QuinnLoewen/Teensy-Synth-Project/Documentation/a-minor-arpeggio.jpg

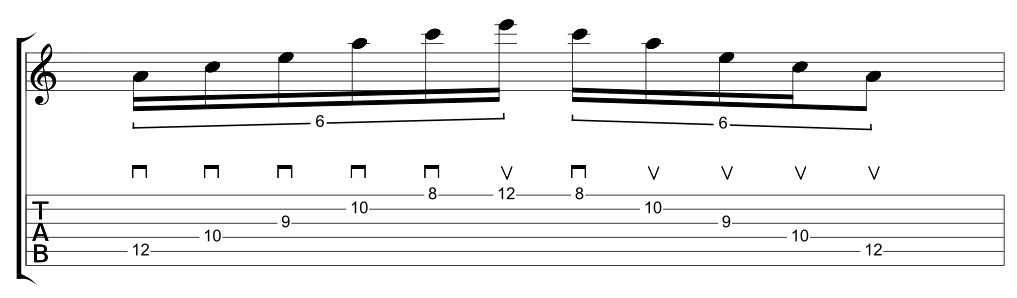
Documentation/a-minor-arpeggio.jpg
