QuinnLoewen/Teensy-Synth-Project/Documentation/Signal Mixing.png

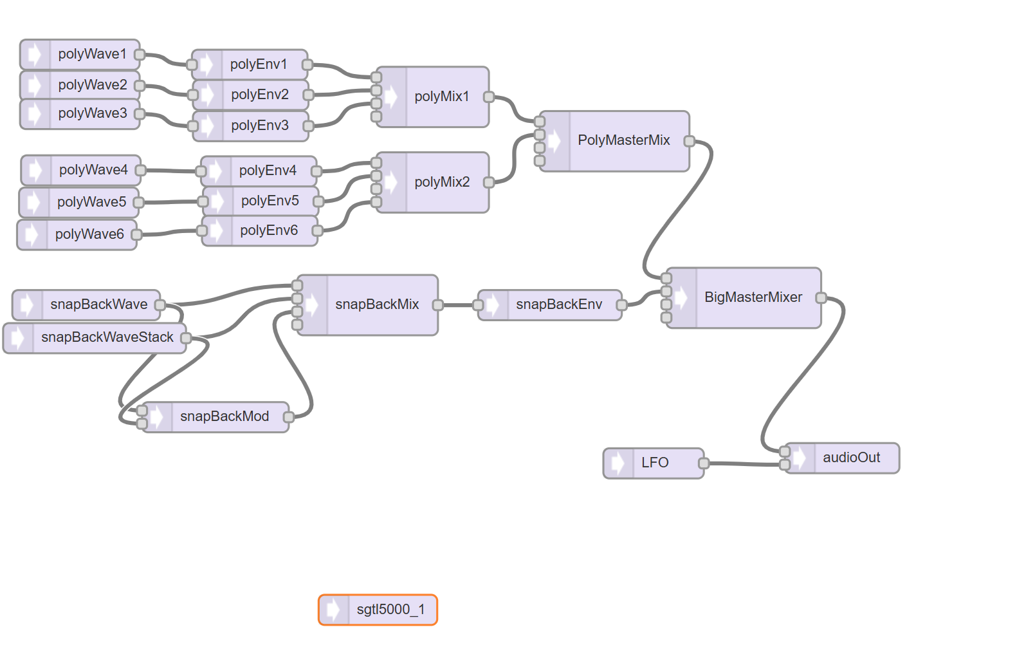
Documentation/Signal Mixing.png
