QuinnLoewen/Teensy-Synth-Project/Documentation/Software_Flowchart.png

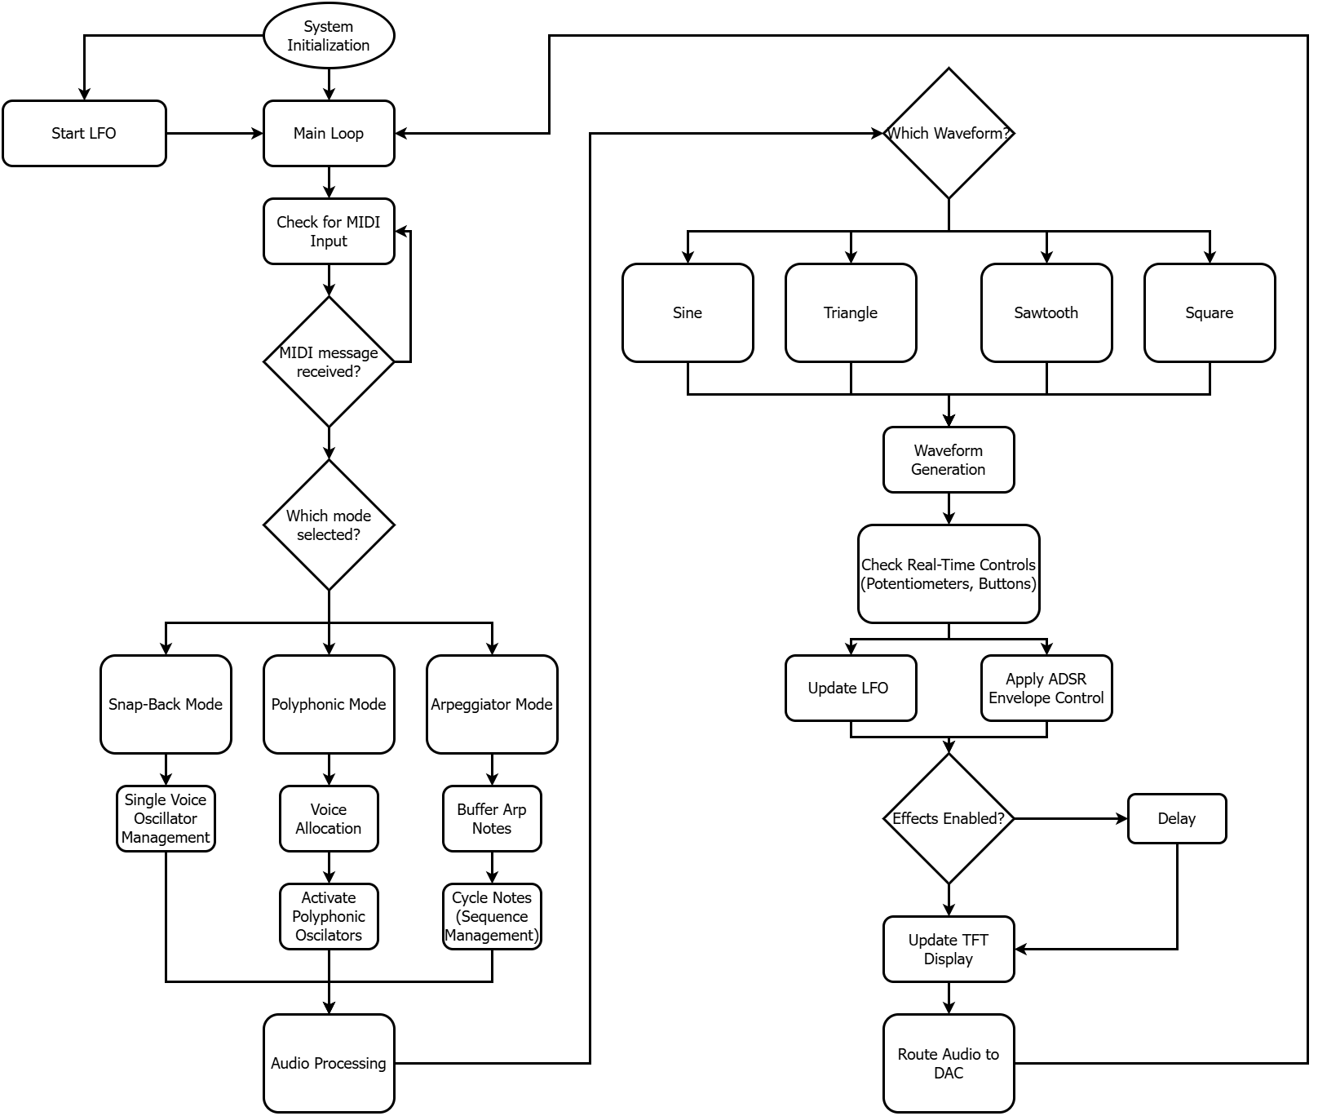
Documentation/Software_Flowchart.png
