QuinnLoewen/Teensy-Synth-Project/Documentation/stackedsine.png

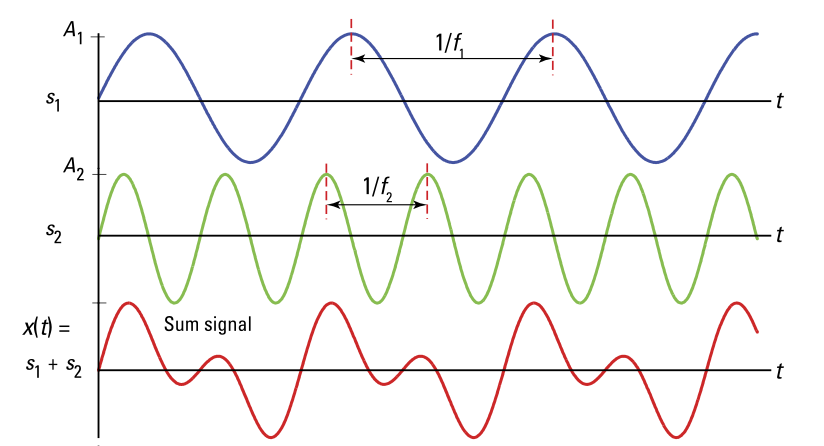
Documentation/stackedsine.png
