QuinnLoewen/Teensy-Synth-Project/Documentation/System_Architecture.png

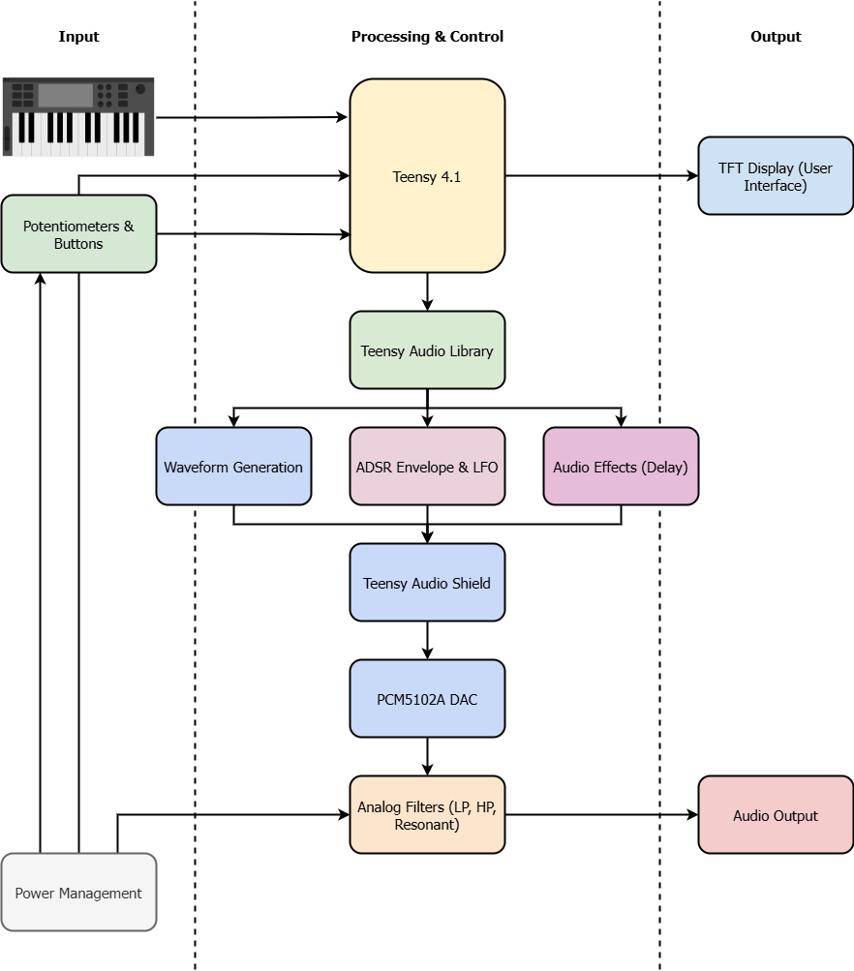
Documentation/System_Architecture.png
