QuinnLoewen/Teensy-Synth-Project/Documentation/waveform_types.png

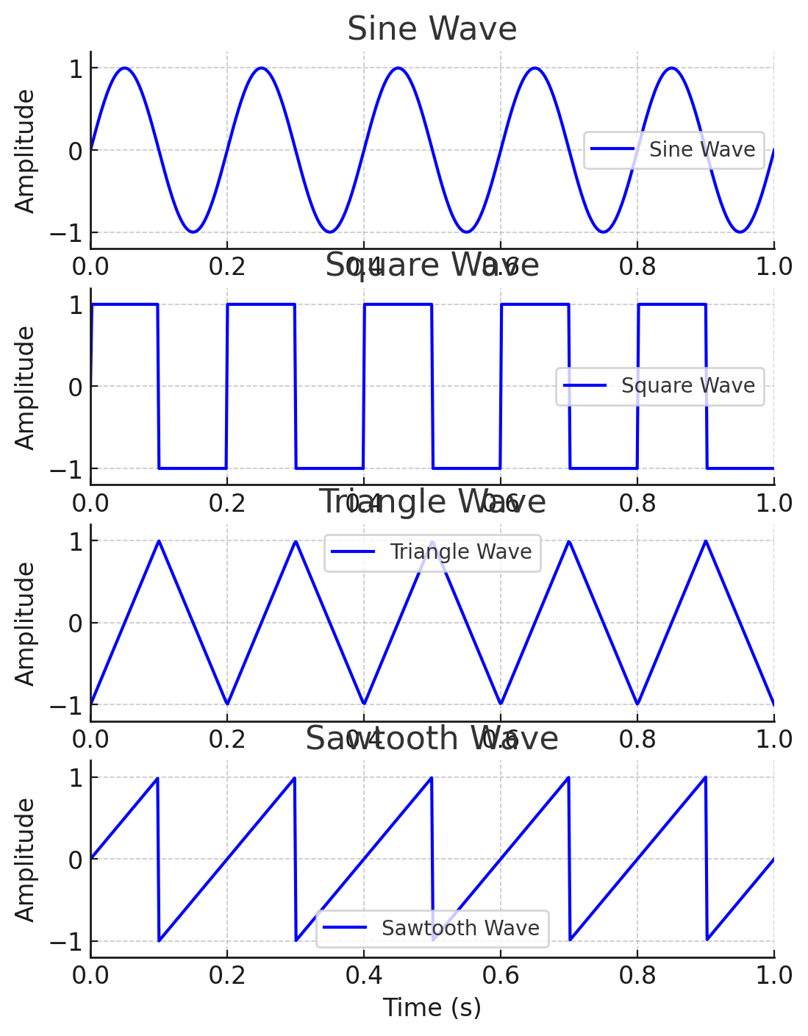
Documentation/waveform_types.png
