QuinnLoewen/Teensy-Synth-Project/Documentation/Waveforms.png

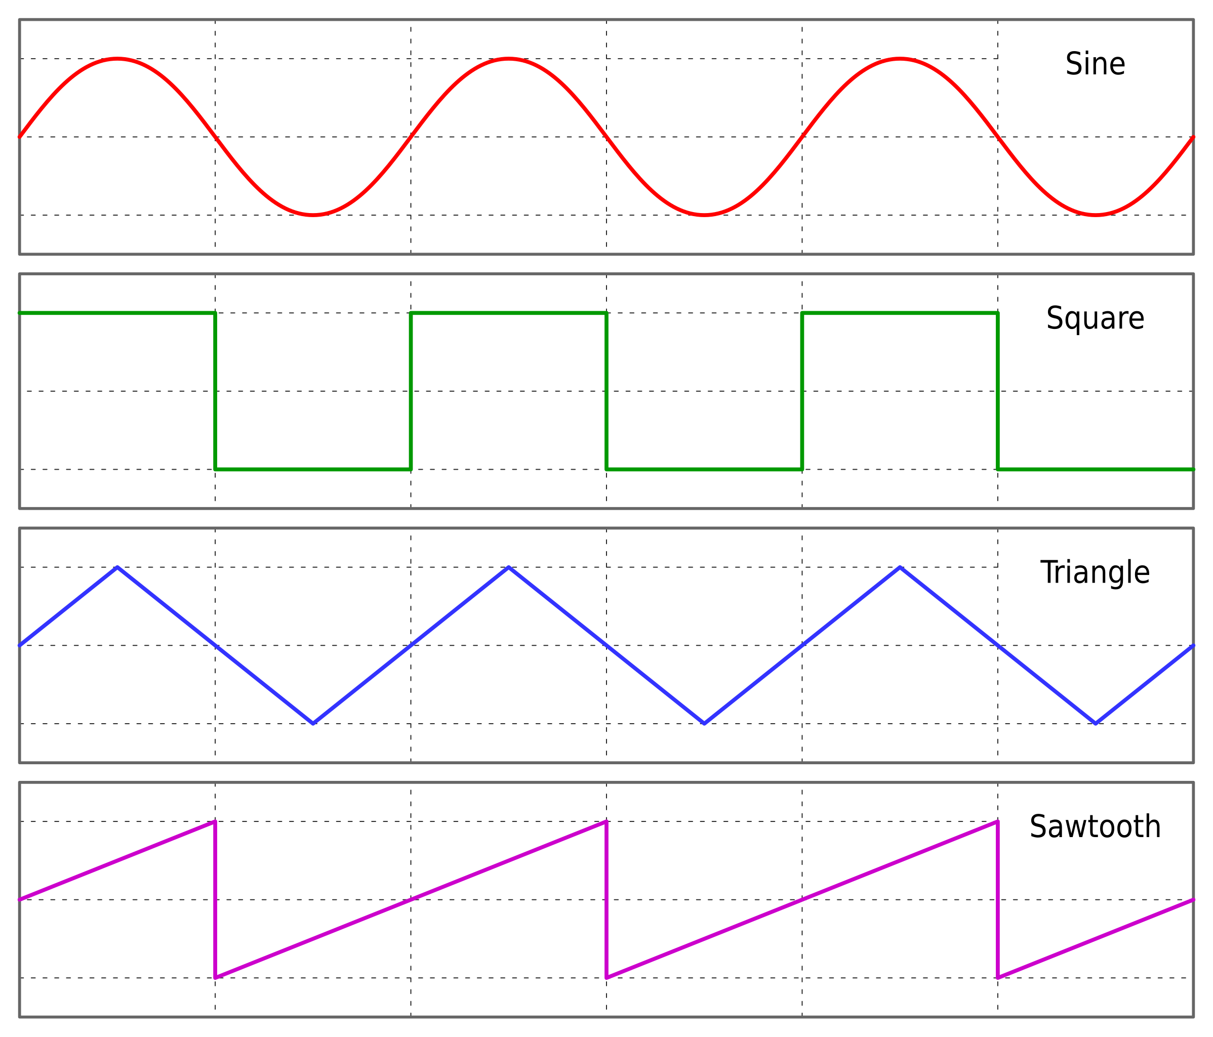
Documentation/Waveforms.png
