QuinnLoewen/Teensy-Synth-Project/Test_Results/Audio_Quality_Tests/synth_performance_metrics.png

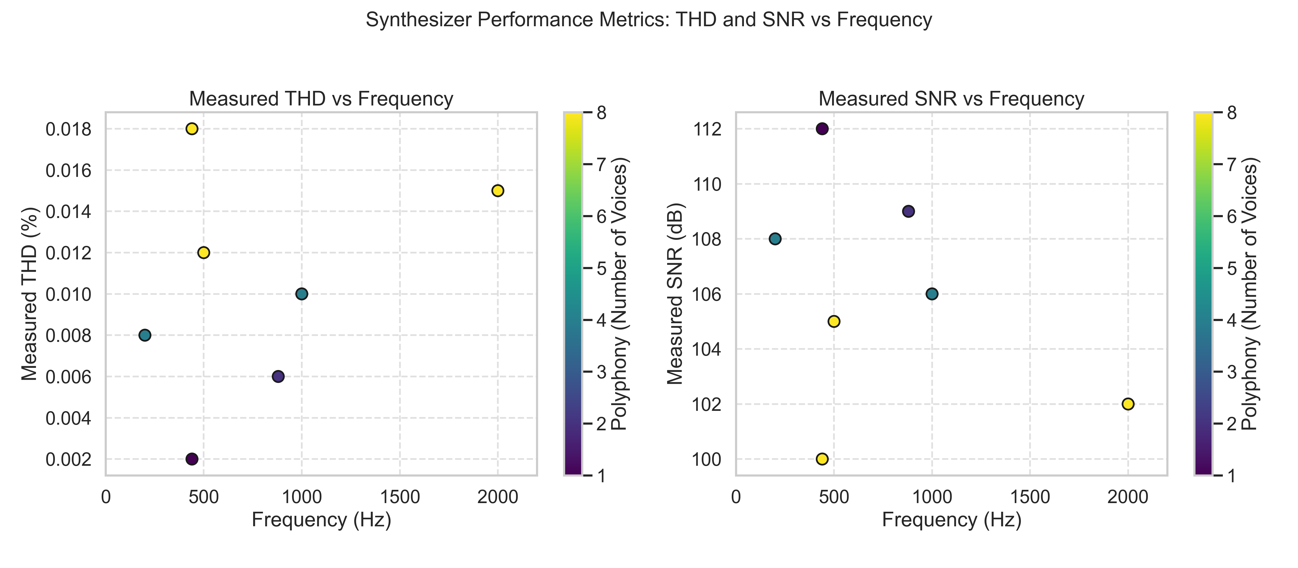
Test_Results/Audio_Quality_Tests/synth_performance_metrics.png
