QuinnLoewen/Teensy-Synth-Project/Test_Results/Filter_Testing/HighPassGraph.png

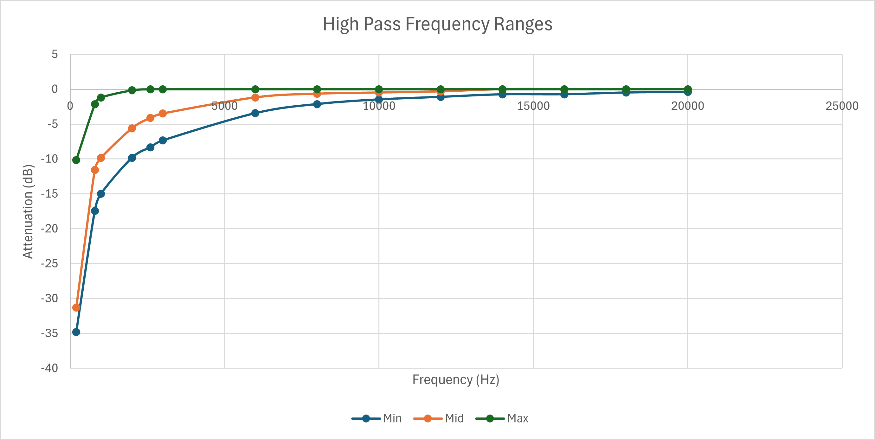
Test_Results/Filter_Testing/HighPassGraph.png
