QuinnLoewen/Teensy-Synth-Project/Test_Results/Filter_Testing/LowPassGraph.png

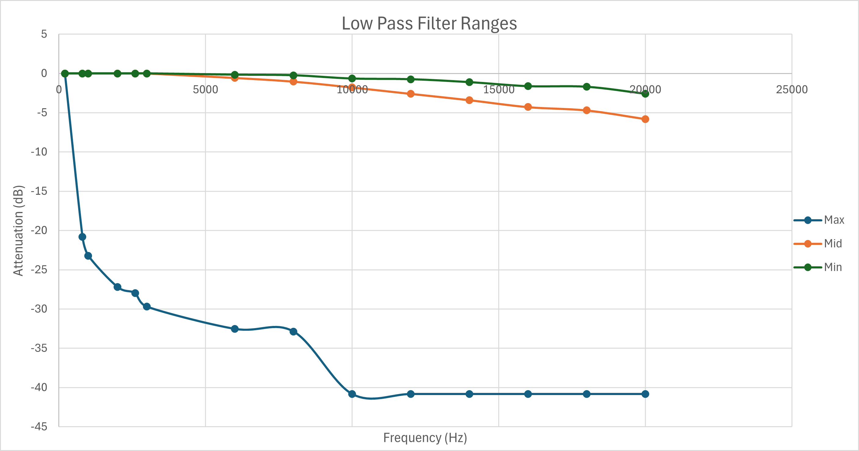
Test_Results/Filter_Testing/LowPassGraph.png
