QuinnLoewen/Teensy-Synth-Project/Test_Results/MIDI_Latency/measuredLatency.png

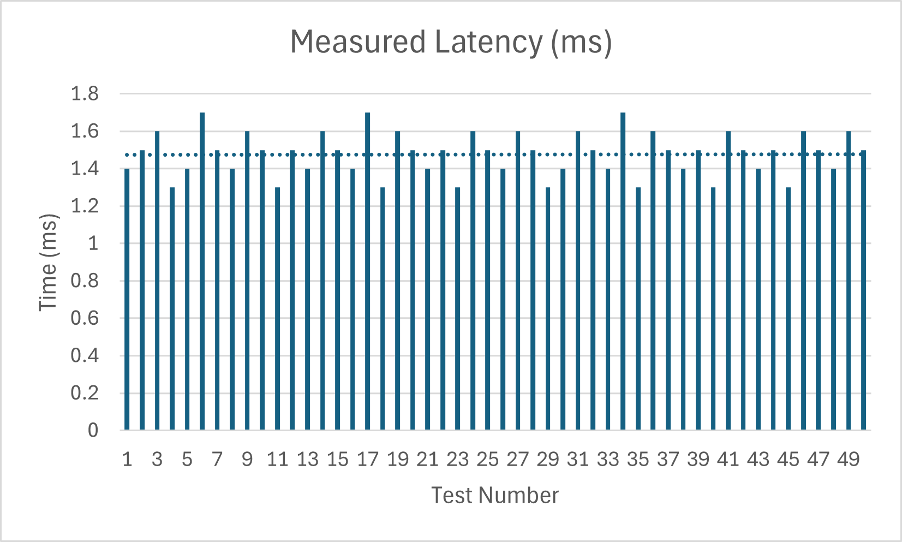
Test_Results/MIDI_Latency/measuredLatency.png
