QuinnLoewen/Teensy-Synth-Project/Test_Results/Note_Frequency_Test/measured_vs_expected_frequency_chart.png

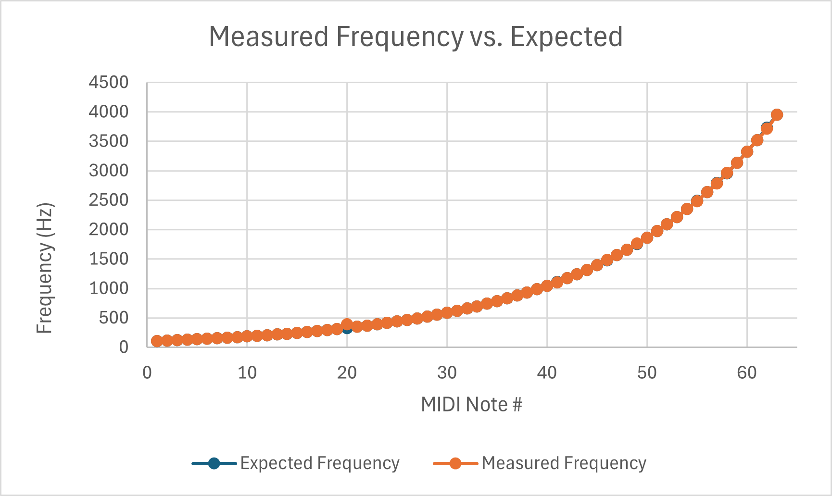
Test_Results/Note_Frequency_Test/measured_vs_expected_frequency_chart.png
