QuinnLoewen/Teensy-Synth-Project/Test_Results/Polyphony_Capacity_Tests/Allwave_vs_CPU.png

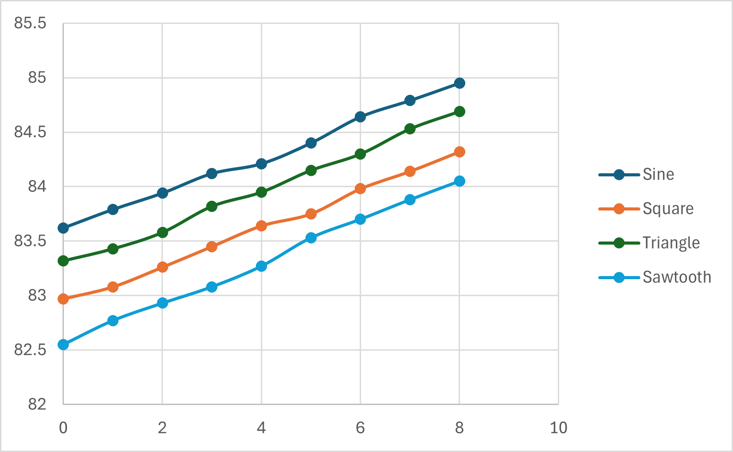
Test_Results/Polyphony_Capacity_Tests/Allwave_vs_CPU.png
