QuinnLoewen/Teensy-Synth-Project/Test_Results/Polyphony_Capacity_Tests/averagecpu.png

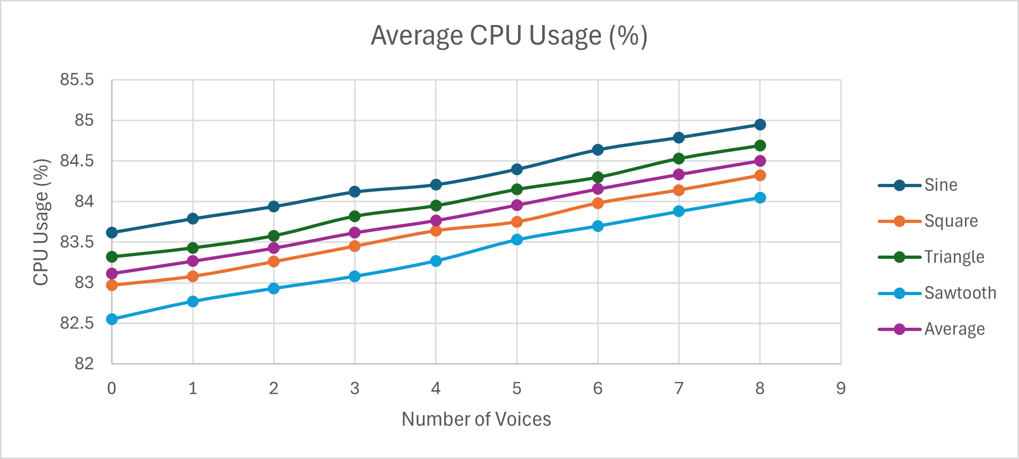
Test_Results/Polyphony_Capacity_Tests/averagecpu.png
