QuinnLoewen/Teensy-Synth-Project/Test_Results/Polyphony_Capacity_Tests/Sawtoothwave_vs_CPU.png

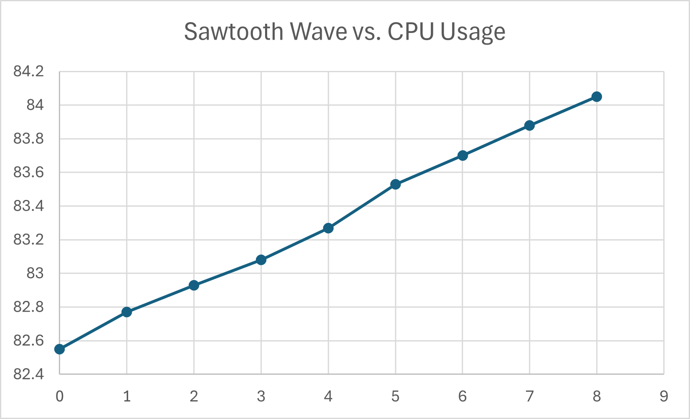
Test_Results/Polyphony_Capacity_Tests/Sawtoothwave_vs_CPU.png
