QuinnLoewen/Teensy-Synth-Project/Test_Results/Polyphony_Capacity_Tests/Sinewave_vs_CPIU.png

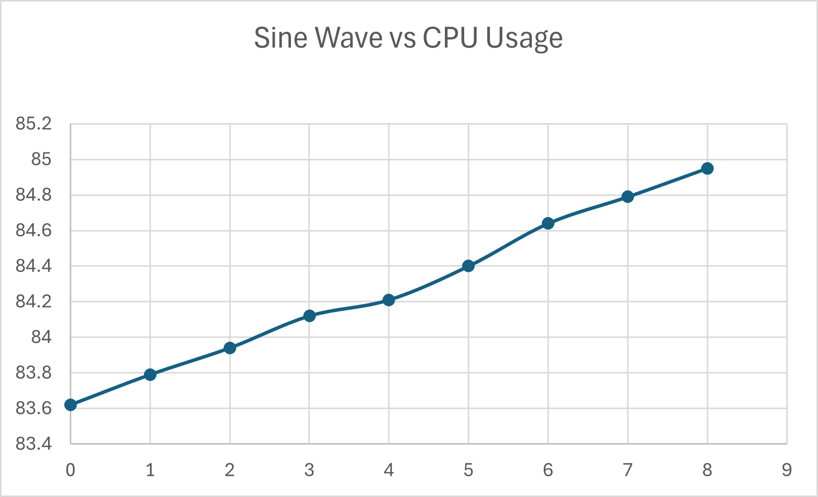
Test_Results/Polyphony_Capacity_Tests/Sinewave_vs_CPIU.png
